wandsonborges/de0-nano-dev/cycloneV_soc/synthesis/cycloneV_soc.vhd

-- cycloneV_soc.vhd

-- Generated using ACDS version 16.1 196

library IEEE;
use IEEE.std_logic_1164.all;
use IEEE.numeric_std.all;

entity cycloneV_soc is
	port (
		adc_clk                         : out   std_logic;                                        --                     adc.clk
		clk_clk                         : in    std_logic                     := '0';             --                     clk.clk
		hps_io_hps_io_emac1_inst_TX_CLK : out   std_logic;                                        --                  hps_io.hps_io_emac1_inst_TX_CLK
		hps_io_hps_io_emac1_inst_TXD0   : out   std_logic;                                        --                        .hps_io_emac1_inst_TXD0
		hps_io_hps_io_emac1_inst_TXD1   : out   std_logic;                                        --                        .hps_io_emac1_inst_TXD1
		hps_io_hps_io_emac1_inst_TXD2   : out   std_logic;                                        --                        .hps_io_emac1_inst_TXD2
		hps_io_hps_io_emac1_inst_TXD3   : out   std_logic;                                        --                        .hps_io_emac1_inst_TXD3
		hps_io_hps_io_emac1_inst_RXD0   : in    std_logic                     := '0';             --                        .hps_io_emac1_inst_RXD0
		hps_io_hps_io_emac1_inst_MDIO   : inout std_logic                     := '0';             --                        .hps_io_emac1_inst_MDIO
		hps_io_hps_io_emac1_inst_MDC    : out   std_logic;                                        --                        .hps_io_emac1_inst_MDC
		hps_io_hps_io_emac1_inst_RX_CTL : in    std_logic                     := '0';             --                        .hps_io_emac1_inst_RX_CTL
		hps_io_hps_io_emac1_inst_TX_CTL : out   std_logic;                                        --                        .hps_io_emac1_inst_TX_CTL
		hps_io_hps_io_emac1_inst_RX_CLK : in    std_logic                     := '0';             --                        .hps_io_emac1_inst_RX_CLK
		hps_io_hps_io_emac1_inst_RXD1   : in    std_logic                     := '0';             --                        .hps_io_emac1_inst_RXD1
		hps_io_hps_io_emac1_inst_RXD2   : in    std_logic                     := '0';             --                        .hps_io_emac1_inst_RXD2
		hps_io_hps_io_emac1_inst_RXD3   : in    std_logic                     := '0';             --                        .hps_io_emac1_inst_RXD3
		hps_io_hps_io_sdio_inst_CMD     : inout std_logic                     := '0';             --                        .hps_io_sdio_inst_CMD
		hps_io_hps_io_sdio_inst_D0      : inout std_logic                     := '0';             --                        .hps_io_sdio_inst_D0
		hps_io_hps_io_sdio_inst_D1      : inout std_logic                     := '0';             --                        .hps_io_sdio_inst_D1
		hps_io_hps_io_sdio_inst_CLK     : out   std_logic;                                        --                        .hps_io_sdio_inst_CLK
		hps_io_hps_io_sdio_inst_D2      : inout std_logic                     := '0';             --                        .hps_io_sdio_inst_D2
		hps_io_hps_io_sdio_inst_D3      : inout std_logic                     := '0';             --                        .hps_io_sdio_inst_D3
		hps_io_hps_io_usb1_inst_D0      : inout std_logic                     := '0';             --                        .hps_io_usb1_inst_D0
		hps_io_hps_io_usb1_inst_D1      : inout std_logic                     := '0';             --                        .hps_io_usb1_inst_D1
		hps_io_hps_io_usb1_inst_D2      : inout std_logic                     := '0';             --                        .hps_io_usb1_inst_D2
		hps_io_hps_io_usb1_inst_D3      : inout std_logic                     := '0';             --                        .hps_io_usb1_inst_D3
		hps_io_hps_io_usb1_inst_D4      : inout std_logic                     := '0';             --                        .hps_io_usb1_inst_D4
		hps_io_hps_io_usb1_inst_D5      : inout std_logic                     := '0';             --                        .hps_io_usb1_inst_D5
		hps_io_hps_io_usb1_inst_D6      : inout std_logic                     := '0';             --                        .hps_io_usb1_inst_D6
		hps_io_hps_io_usb1_inst_D7      : inout std_logic                     := '0';             --                        .hps_io_usb1_inst_D7
		hps_io_hps_io_usb1_inst_CLK     : in    std_logic                     := '0';             --                        .hps_io_usb1_inst_CLK
		hps_io_hps_io_usb1_inst_STP     : out   std_logic;                                        --                        .hps_io_usb1_inst_STP
		hps_io_hps_io_usb1_inst_DIR     : in    std_logic                     := '0';             --                        .hps_io_usb1_inst_DIR
		hps_io_hps_io_usb1_inst_NXT     : in    std_logic                     := '0';             --                        .hps_io_usb1_inst_NXT
		hps_io_hps_io_uart0_inst_RX     : in    std_logic                     := '0';             --                        .hps_io_uart0_inst_RX
		hps_io_hps_io_uart0_inst_TX     : out   std_logic;                                        --                        .hps_io_uart0_inst_TX
		i2c_SCL                         : out   std_logic;                                        --                     i2c.SCL
		i2c_SDA                         : inout std_logic                     := '0';             --                        .SDA
		led_external_connection_export  : out   std_logic_vector(7 downto 0);                     -- led_external_connection.export
		mc_clk                          : out   std_logic;                                        --                      mc.clk
		memory_mem_a                    : out   std_logic_vector(14 downto 0);                    --                  memory.mem_a
		memory_mem_ba                   : out   std_logic_vector(2 downto 0);                     --                        .mem_ba
		memory_mem_ck                   : out   std_logic;                                        --                        .mem_ck
		memory_mem_ck_n                 : out   std_logic;                                        --                        .mem_ck_n
		memory_mem_cke                  : out   std_logic;                                        --                        .mem_cke
		memory_mem_cs_n                 : out   std_logic;                                        --                        .mem_cs_n
		memory_mem_ras_n                : out   std_logic;                                        --                        .mem_ras_n
		memory_mem_cas_n                : out   std_logic;                                        --                        .mem_cas_n
		memory_mem_we_n                 : out   std_logic;                                        --                        .mem_we_n
		memory_mem_reset_n              : out   std_logic;                                        --                        .mem_reset_n
		memory_mem_dq                   : inout std_logic_vector(31 downto 0) := (others => '0'); --                        .mem_dq
		memory_mem_dqs                  : inout std_logic_vector(3 downto 0)  := (others => '0'); --                        .mem_dqs
		memory_mem_dqs_n                : inout std_logic_vector(3 downto 0)  := (others => '0'); --                        .mem_dqs_n
		memory_mem_odt                  : out   std_logic;                                        --                        .mem_odt
		memory_mem_dm                   : out   std_logic_vector(3 downto 0);                     --                        .mem_dm
		memory_oct_rzqin                : in    std_logic                     := '0';             --                        .oct_rzqin
		pico640_PSYNC                   : in    std_logic                     := '0';             --                 pico640.PSYNC
		pico640_VSYNC                   : in    std_logic                     := '0';             --                        .VSYNC
		pico640_HSYNC                   : in    std_logic                     := '0';             --                        .HSYNC
		pico640_ADC_DATA                : in    std_logic_vector(13 downto 0) := (others => '0'); --                        .ADC_DATA
		pico640_SHUTTER                 : out   std_logic;                                        --                        .SHUTTER
		pico640_SENSOR_RST_N            : out   std_logic;                                        --                        .SENSOR_RST_N
		pico640_CLOCK_EN                : out   std_logic;                                        --                        .CLOCK_EN
		pio_export                      : out   std_logic_vector(7 downto 0);                     --                     pio.export
		reset_reset_n                   : in    std_logic                     := '0';             --                   reset.reset_n
		sw_external_connection_export   : in    std_logic_vector(3 downto 0)  := (others => '0')  --  sw_external_connection.export
	);
end entity cycloneV_soc;

architecture rtl of cycloneV_soc is
	component framewriter is
		generic (
			CLOCK_FREQ         : integer := 50000000;
			NBITS_DATA         : integer := 8;
			BURST_LENGTH_DEPTH : integer := 3;
			FIFO_DEPTH         : integer := 10
		);
		port (
			avalon_ss_clk           : in  std_logic                     := 'X';             -- clk
			avalon_mm_clk           : in  std_logic                     := 'X';             -- clk
			avalon_st_clk           : in  std_logic                     := 'X';             -- clk
			avalon_ss_rstn          : in  std_logic                     := 'X';             -- reset_n
			avalon_mm_rstn          : in  std_logic                     := 'X';             -- reset_n
			avalon_st_rstn          : in  std_logic                     := 'X';             -- reset_n
			avalon_mm_address       : out std_logic_vector(31 downto 0);                    -- address
			avalon_mm_burstcount    : out std_logic_vector(7 downto 0);                     -- burstcount
			avalon_mm_write         : out std_logic;                                        -- write
			avalon_mm_writedata     : out std_logic_vector(15 downto 0);                    -- writedata
			avalon_mm_waitrequest   : in  std_logic                     := 'X';             -- waitrequest
			avalon_ss_address       : in  std_logic_vector(2 downto 0)  := (others => 'X'); -- address
			avalon_ss_read          : in  std_logic                     := 'X';             -- read
			avalon_ss_readdata      : out std_logic_vector(31 downto 0);                    -- readdata
			avalon_ss_waitrequest   : out std_logic;                                        -- waitrequest
			avalon_ss_readdatavalid : out std_logic;                                        -- readdatavalid
			avalon_ss_write         : in  std_logic                     := 'X';             -- write
			avalon_ss_writedata     : in  std_logic_vector(31 downto 0) := (others => 'X'); -- writedata
			avalon_st_data          : in  std_logic_vector(15 downto 0) := (others => 'X'); -- data
			avalon_st_endofpacket   : in  std_logic                     := 'X';             -- endofpacket
			avalon_st_ready         : out std_logic;                                        -- ready
			avalon_st_startofpacket : in  std_logic                     := 'X';             -- startofpacket
			avalon_st_valid         : in  std_logic                     := 'X'              -- valid
		);
	end component framewriter;

	component cycloneV_soc_hps_0 is
		generic (
			F2S_Width : integer := 2;
			S2F_Width : integer := 2
		);
		port (
			mem_a                    : out   std_logic_vector(14 downto 0);                     -- mem_a
			mem_ba                   : out   std_logic_vector(2 downto 0);                      -- mem_ba
			mem_ck                   : out   std_logic;                                         -- mem_ck
			mem_ck_n                 : out   std_logic;                                         -- mem_ck_n
			mem_cke                  : out   std_logic;                                         -- mem_cke
			mem_cs_n                 : out   std_logic;                                         -- mem_cs_n
			mem_ras_n                : out   std_logic;                                         -- mem_ras_n
			mem_cas_n                : out   std_logic;                                         -- mem_cas_n
			mem_we_n                 : out   std_logic;                                         -- mem_we_n
			mem_reset_n              : out   std_logic;                                         -- mem_reset_n
			mem_dq                   : inout std_logic_vector(31 downto 0)  := (others => 'X'); -- mem_dq
			mem_dqs                  : inout std_logic_vector(3 downto 0)   := (others => 'X'); -- mem_dqs
			mem_dqs_n                : inout std_logic_vector(3 downto 0)   := (others => 'X'); -- mem_dqs_n
			mem_odt                  : out   std_logic;                                         -- mem_odt
			mem_dm                   : out   std_logic_vector(3 downto 0);                      -- mem_dm
			oct_rzqin                : in    std_logic                      := 'X';             -- oct_rzqin
			hps_io_emac1_inst_TX_CLK : out   std_logic;                                         -- hps_io_emac1_inst_TX_CLK
			hps_io_emac1_inst_TXD0   : out   std_logic;                                         -- hps_io_emac1_inst_TXD0
			hps_io_emac1_inst_TXD1   : out   std_logic;                                         -- hps_io_emac1_inst_TXD1
			hps_io_emac1_inst_TXD2   : out   std_logic;                                         -- hps_io_emac1_inst_TXD2
			hps_io_emac1_inst_TXD3   : out   std_logic;                                         -- hps_io_emac1_inst_TXD3
			hps_io_emac1_inst_RXD0   : in    std_logic                      := 'X';             -- hps_io_emac1_inst_RXD0
			hps_io_emac1_inst_MDIO   : inout std_logic                      := 'X';             -- hps_io_emac1_inst_MDIO
			hps_io_emac1_inst_MDC    : out   std_logic;                                         -- hps_io_emac1_inst_MDC
			hps_io_emac1_inst_RX_CTL : in    std_logic                      := 'X';             -- hps_io_emac1_inst_RX_CTL
			hps_io_emac1_inst_TX_CTL : out   std_logic;                                         -- hps_io_emac1_inst_TX_CTL
			hps_io_emac1_inst_RX_CLK : in    std_logic                      := 'X';             -- hps_io_emac1_inst_RX_CLK
			hps_io_emac1_inst_RXD1   : in    std_logic                      := 'X';             -- hps_io_emac1_inst_RXD1
			hps_io_emac1_inst_RXD2   : in    std_logic                      := 'X';             -- hps_io_emac1_inst_RXD2
			hps_io_emac1_inst_RXD3   : in    std_logic                      := 'X';             -- hps_io_emac1_inst_RXD3
			hps_io_sdio_inst_CMD     : inout std_logic                      := 'X';             -- hps_io_sdio_inst_CMD
			hps_io_sdio_inst_D0      : inout std_logic                      := 'X';             -- hps_io_sdio_inst_D0
			hps_io_sdio_inst_D1      : inout std_logic                      := 'X';             -- hps_io_sdio_inst_D1
			hps_io_sdio_inst_CLK     : out   std_logic;                                         -- hps_io_sdio_inst_CLK
			hps_io_sdio_inst_D2      : inout std_logic                      := 'X';             -- hps_io_sdio_inst_D2
			hps_io_sdio_inst_D3      : inout std_logic                      := 'X';             -- hps_io_sdio_inst_D3
			hps_io_usb1_inst_D0      : inout std_logic                      := 'X';             -- hps_io_usb1_inst_D0
			hps_io_usb1_inst_D1      : inout std_logic                      := 'X';             -- hps_io_usb1_inst_D1
			hps_io_usb1_inst_D2      : inout std_logic                      := 'X';             -- hps_io_usb1_inst_D2
			hps_io_usb1_inst_D3      : inout std_logic                      := 'X';             -- hps_io_usb1_inst_D3
			hps_io_usb1_inst_D4      : inout std_logic                      := 'X';             -- hps_io_usb1_inst_D4
			hps_io_usb1_inst_D5      : inout std_logic                      := 'X';             -- hps_io_usb1_inst_D5
			hps_io_usb1_inst_D6      : inout std_logic                      := 'X';             -- hps_io_usb1_inst_D6
			hps_io_usb1_inst_D7      : inout std_logic                      := 'X';             -- hps_io_usb1_inst_D7
			hps_io_usb1_inst_CLK     : in    std_logic                      := 'X';             -- hps_io_usb1_inst_CLK
			hps_io_usb1_inst_STP     : out   std_logic;                                         -- hps_io_usb1_inst_STP
			hps_io_usb1_inst_DIR     : in    std_logic                      := 'X';             -- hps_io_usb1_inst_DIR
			hps_io_usb1_inst_NXT     : in    std_logic                      := 'X';             -- hps_io_usb1_inst_NXT
			hps_io_uart0_inst_RX     : in    std_logic                      := 'X';             -- hps_io_uart0_inst_RX
			hps_io_uart0_inst_TX     : out   std_logic;                                         -- hps_io_uart0_inst_TX
			h2f_rst_n                : out   std_logic;                                         -- reset_n
			f2h_sdram0_clk           : in    std_logic                      := 'X';             -- clk
			f2h_sdram0_ADDRESS       : in    std_logic_vector(26 downto 0)  := (others => 'X'); -- address
			f2h_sdram0_BURSTCOUNT    : in    std_logic_vector(7 downto 0)   := (others => 'X'); -- burstcount
			f2h_sdram0_WAITREQUEST   : out   std_logic;                                         -- waitrequest
			f2h_sdram0_WRITEDATA     : in    std_logic_vector(255 downto 0) := (others => 'X'); -- writedata
			f2h_sdram0_BYTEENABLE    : in    std_logic_vector(31 downto 0)  := (others => 'X'); -- byteenable
			f2h_sdram0_WRITE         : in    std_logic                      := 'X';             -- write
			h2f_axi_clk              : in    std_logic                      := 'X';             -- clk
			h2f_AWID                 : out   std_logic_vector(11 downto 0);                     -- awid
			h2f_AWADDR               : out   std_logic_vector(29 downto 0);                     -- awaddr
			h2f_AWLEN                : out   std_logic_vector(3 downto 0);                      -- awlen
			h2f_AWSIZE               : out   std_logic_vector(2 downto 0);                      -- awsize
			h2f_AWBURST              : out   std_logic_vector(1 downto 0);                      -- awburst
			h2f_AWLOCK               : out   std_logic_vector(1 downto 0);                      -- awlock
			h2f_AWCACHE              : out   std_logic_vector(3 downto 0);                      -- awcache
			h2f_AWPROT               : out   std_logic_vector(2 downto 0);                      -- awprot
			h2f_AWVALID              : out   std_logic;                                         -- awvalid
			h2f_AWREADY              : in    std_logic                      := 'X';             -- awready
			h2f_WID                  : out   std_logic_vector(11 downto 0);                     -- wid
			h2f_WDATA                : out   std_logic_vector(63 downto 0);                     -- wdata
			h2f_WSTRB                : out   std_logic_vector(7 downto 0);                      -- wstrb
			h2f_WLAST                : out   std_logic;                                         -- wlast
			h2f_WVALID               : out   std_logic;                                         -- wvalid
			h2f_WREADY               : in    std_logic                      := 'X';             -- wready
			h2f_BID                  : in    std_logic_vector(11 downto 0)  := (others => 'X'); -- bid
			h2f_BRESP                : in    std_logic_vector(1 downto 0)   := (others => 'X'); -- bresp
			h2f_BVALID               : in    std_logic                      := 'X';             -- bvalid
			h2f_BREADY               : out   std_logic;                                         -- bready
			h2f_ARID                 : out   std_logic_vector(11 downto 0);                     -- arid
			h2f_ARADDR               : out   std_logic_vector(29 downto 0);                     -- araddr
			h2f_ARLEN                : out   std_logic_vector(3 downto 0);                      -- arlen
			h2f_ARSIZE               : out   std_logic_vector(2 downto 0);                      -- arsize
			h2f_ARBURST              : out   std_logic_vector(1 downto 0);                      -- arburst
			h2f_ARLOCK               : out   std_logic_vector(1 downto 0);                      -- arlock
			h2f_ARCACHE              : out   std_logic_vector(3 downto 0);                      -- arcache
			h2f_ARPROT               : out   std_logic_vector(2 downto 0);                      -- arprot
			h2f_ARVALID              : out   std_logic;                                         -- arvalid
			h2f_ARREADY              : in    std_logic                      := 'X';             -- arready
			h2f_RID                  : in    std_logic_vector(11 downto 0)  := (others => 'X'); -- rid
			h2f_RDATA                : in    std_logic_vector(63 downto 0)  := (others => 'X'); -- rdata
			h2f_RRESP                : in    std_logic_vector(1 downto 0)   := (others => 'X'); -- rresp
			h2f_RLAST                : in    std_logic                      := 'X';             -- rlast
			h2f_RVALID               : in    std_logic                      := 'X';             -- rvalid
			h2f_RREADY               : out   std_logic;                                         -- rready
			f2h_axi_clk              : in    std_logic                      := 'X';             -- clk
			f2h_AWID                 : in    std_logic_vector(7 downto 0)   := (others => 'X'); -- awid
			f2h_AWADDR               : in    std_logic_vector(31 downto 0)  := (others => 'X'); -- awaddr
			f2h_AWLEN                : in    std_logic_vector(3 downto 0)   := (others => 'X'); -- awlen
			f2h_AWSIZE               : in    std_logic_vector(2 downto 0)   := (others => 'X'); -- awsize
			f2h_AWBURST              : in    std_logic_vector(1 downto 0)   := (others => 'X'); -- awburst
			f2h_AWLOCK               : in    std_logic_vector(1 downto 0)   := (others => 'X'); -- awlock
			f2h_AWCACHE              : in    std_logic_vector(3 downto 0)   := (others => 'X'); -- awcache
			f2h_AWPROT               : in    std_logic_vector(2 downto 0)   := (others => 'X'); -- awprot
			f2h_AWVALID              : in    std_logic                      := 'X';             -- awvalid
			f2h_AWREADY              : out   std_logic;                                         -- awready
			f2h_AWUSER               : in    std_logic_vector(4 downto 0)   := (others => 'X'); -- awuser
			f2h_WID                  : in    std_logic_vector(7 downto 0)   := (others => 'X'); -- wid
			f2h_WDATA                : in    std_logic_vector(127 downto 0) := (others => 'X'); -- wdata
			f2h_WSTRB                : in    std_logic_vector(15 downto 0)  := (others => 'X'); -- wstrb
			f2h_WLAST                : in    std_logic                      := 'X';             -- wlast
			f2h_WVALID               : in    std_logic                      := 'X';             -- wvalid
			f2h_WREADY               : out   std_logic;                                         -- wready
			f2h_BID                  : out   std_logic_vector(7 downto 0);                      -- bid
			f2h_BRESP                : out   std_logic_vector(1 downto 0);                      -- bresp
			f2h_BVALID               : out   std_logic;                                         -- bvalid
			f2h_BREADY               : in    std_logic                      := 'X';             -- bready
			f2h_ARID                 : in    std_logic_vector(7 downto 0)   := (others => 'X'); -- arid
			f2h_ARADDR               : in    std_logic_vector(31 downto 0)  := (others => 'X'); -- araddr
			f2h_ARLEN                : in    std_logic_vector(3 downto 0)   := (others => 'X'); -- arlen
			f2h_ARSIZE               : in    std_logic_vector(2 downto 0)   := (others => 'X'); -- arsize
			f2h_ARBURST              : in    std_logic_vector(1 downto 0)   := (others => 'X'); -- arburst
			f2h_ARLOCK               : in    std_logic_vector(1 downto 0)   := (others => 'X'); -- arlock
			f2h_ARCACHE              : in    std_logic_vector(3 downto 0)   := (others => 'X'); -- arcache
			f2h_ARPROT               : in    std_logic_vector(2 downto 0)   := (others => 'X'); -- arprot
			f2h_ARVALID              : in    std_logic                      := 'X';             -- arvalid
			f2h_ARREADY              : out   std_logic;                                         -- arready
			f2h_ARUSER               : in    std_logic_vector(4 downto 0)   := (others => 'X'); -- aruser
			f2h_RID                  : out   std_logic_vector(7 downto 0);                      -- rid
			f2h_RDATA                : out   std_logic_vector(127 downto 0);                    -- rdata
			f2h_RRESP                : out   std_logic_vector(1 downto 0);                      -- rresp
			f2h_RLAST                : out   std_logic;                                         -- rlast
			f2h_RVALID               : out   std_logic;                                         -- rvalid
			f2h_RREADY               : in    std_logic                      := 'X';             -- rready
			h2f_lw_axi_clk           : in    std_logic                      := 'X';             -- clk
			h2f_lw_AWID              : out   std_logic_vector(11 downto 0);                     -- awid
			h2f_lw_AWADDR            : out   std_logic_vector(20 downto 0);                     -- awaddr
			h2f_lw_AWLEN             : out   std_logic_vector(3 downto 0);                      -- awlen
			h2f_lw_AWSIZE            : out   std_logic_vector(2 downto 0);                      -- awsize
			h2f_lw_AWBURST           : out   std_logic_vector(1 downto 0);                      -- awburst
			h2f_lw_AWLOCK            : out   std_logic_vector(1 downto 0);                      -- awlock
			h2f_lw_AWCACHE           : out   std_logic_vector(3 downto 0);                      -- awcache
			h2f_lw_AWPROT            : out   std_logic_vector(2 downto 0);                      -- awprot
			h2f_lw_AWVALID           : out   std_logic;                                         -- awvalid
			h2f_lw_AWREADY           : in    std_logic                      := 'X';             -- awready
			h2f_lw_WID               : out   std_logic_vector(11 downto 0);                     -- wid
			h2f_lw_WDATA             : out   std_logic_vector(31 downto 0);                     -- wdata
			h2f_lw_WSTRB             : out   std_logic_vector(3 downto 0);                      -- wstrb
			h2f_lw_WLAST             : out   std_logic;                                         -- wlast
			h2f_lw_WVALID            : out   std_logic;                                         -- wvalid
			h2f_lw_WREADY            : in    std_logic                      := 'X';             -- wready
			h2f_lw_BID               : in    std_logic_vector(11 downto 0)  := (others => 'X'); -- bid
			h2f_lw_BRESP             : in    std_logic_vector(1 downto 0)   := (others => 'X'); -- bresp
			h2f_lw_BVALID            : in    std_logic                      := 'X';             -- bvalid
			h2f_lw_BREADY            : out   std_logic;                                         -- bready
			h2f_lw_ARID              : out   std_logic_vector(11 downto 0);                     -- arid
			h2f_lw_ARADDR            : out   std_logic_vector(20 downto 0);                     -- araddr
			h2f_lw_ARLEN             : out   std_logic_vector(3 downto 0);                      -- arlen
			h2f_lw_ARSIZE            : out   std_logic_vector(2 downto 0);                      -- arsize
			h2f_lw_ARBURST           : out   std_logic_vector(1 downto 0);                      -- arburst
			h2f_lw_ARLOCK            : out   std_logic_vector(1 downto 0);                      -- arlock
			h2f_lw_ARCACHE           : out   std_logic_vector(3 downto 0);                      -- arcache
			h2f_lw_ARPROT            : out   std_logic_vector(2 downto 0);                      -- arprot
			h2f_lw_ARVALID           : out   std_logic;                                         -- arvalid
			h2f_lw_ARREADY           : in    std_logic                      := 'X';             -- arready
			h2f_lw_RID               : in    std_logic_vector(11 downto 0)  := (others => 'X'); -- rid
			h2f_lw_RDATA             : in    std_logic_vector(31 downto 0)  := (others => 'X'); -- rdata
			h2f_lw_RRESP             : in    std_logic_vector(1 downto 0)   := (others => 'X'); -- rresp
			h2f_lw_RLAST             : in    std_logic                      := 'X';             -- rlast
			h2f_lw_RVALID            : in    std_logic                      := 'X';             -- rvalid
			h2f_lw_RREADY            : out   std_logic                                          -- rready
		);
	end component cycloneV_soc_hps_0;

	component i2c_master_avalon is
		generic (
			CLOCK_FREQ   : integer := 70000000;
			I2C_CLK_FREQ : integer := 200000;
			CHECK_ACK    : boolean := true
		);
		port (
			clk                 : in    std_logic                     := 'X';             -- clk
			slave_chipselect    : in    std_logic                     := 'X';             -- chipselect
			slave_write         : in    std_logic                     := 'X';             -- write
			slave_address       : in    std_logic_vector(3 downto 0)  := (others => 'X'); -- address
			slave_writedata     : in    std_logic_vector(31 downto 0) := (others => 'X'); -- writedata
			slave_waitrequest   : out   std_logic;                                        -- waitrequest
			slave_readdatavalid : out   std_logic;                                        -- readdatavalid
			slave_readdata      : out   std_logic_vector(31 downto 0);                    -- readdata
			slave_read          : in    std_logic                     := 'X';             -- read
			rst_n               : in    std_logic                     := 'X';             -- reset_n
			SCL                 : out   std_logic;                                        -- export
			SDA                 : inout std_logic                     := 'X'              -- export
		);
	end component i2c_master_avalon;

	component cycloneV_soc_led is
		port (
			clk        : in  std_logic                     := 'X';             -- clk
			reset_n    : in  std_logic                     := 'X';             -- reset_n
			address    : in  std_logic_vector(1 downto 0)  := (others => 'X'); -- address
			write_n    : in  std_logic                     := 'X';             -- write_n
			writedata  : in  std_logic_vector(31 downto 0) := (others => 'X'); -- writedata
			chipselect : in  std_logic                     := 'X';             -- chipselect
			readdata   : out std_logic_vector(31 downto 0);                    -- readdata
			out_port   : out std_logic_vector(7 downto 0)                      -- export
		);
	end component cycloneV_soc_led;

	component pico640_avalon is
		generic (
			SENSOR_CLOCK : integer := 12000000
		);
		port (
			PSYNC                   : in  std_logic                     := 'X';             -- export
			VSYNC                   : in  std_logic                     := 'X';             -- export
			HSYNC                   : in  std_logic                     := 'X';             -- export
			ADC_DATA                : in  std_logic_vector(13 downto 0) := (others => 'X'); -- export
			SHUTTER                 : out std_logic;                                        -- export
			SENSOR_RST_N            : out std_logic;                                        -- export
			CLOCK_EN                : out std_logic;                                        -- export
			avalon_ss_clk           : in  std_logic                     := 'X';             -- clk
			master_clk              : in  std_logic                     := 'X';             -- clk
			avalon_ss_rstn          : in  std_logic                     := 'X';             -- reset_n
			master_rstn             : in  std_logic                     := 'X';             -- reset_n
			avalon_st_startofpacket : out std_logic;                                        -- startofpacket
			avalon_st_endofpacket   : out std_logic;                                        -- endofpacket
			avalon_st_valid         : out std_logic;                                        -- valid
			avalon_st_data          : out std_logic_vector(15 downto 0);                    -- data
			avalon_st_ready         : in  std_logic                     := 'X';             -- ready
			slave_write             : in  std_logic                     := 'X';             -- write
			slave_address           : in  std_logic_vector(2 downto 0)  := (others => 'X'); -- address
			slave_writedata         : in  std_logic_vector(31 downto 0) := (others => 'X'); -- writedata
			slave_waitrequest       : out std_logic;                                        -- waitrequest
			slave_readdatavalid     : out std_logic;                                        -- readdatavalid
			slave_readdata          : out std_logic_vector(31 downto 0);                    -- readdata
			slave_read              : in  std_logic                     := 'X'              -- read
		);
	end component pico640_avalon;

	component cycloneV_soc_pll_0 is
		port (
			refclk   : in  std_logic := 'X'; -- clk
			rst      : in  std_logic := 'X'; -- reset
			outclk_0 : out std_logic;        -- clk
			outclk_1 : out std_logic;        -- clk
			locked   : out std_logic         -- export
		);
	end component cycloneV_soc_pll_0;

	component cycloneV_soc_sw is
		port (
			clk      : in  std_logic                     := 'X';             -- clk
			reset_n  : in  std_logic                     := 'X';             -- reset_n
			address  : in  std_logic_vector(1 downto 0)  := (others => 'X'); -- address
			readdata : out std_logic_vector(31 downto 0);                    -- readdata
			in_port  : in  std_logic_vector(3 downto 0)  := (others => 'X')  -- export
		);
	end component cycloneV_soc_sw;

	component cycloneV_soc_mm_interconnect_0 is
		port (
			clock_50_clk_clk                                                   : in  std_logic                      := 'X';             -- clk
			framewriter_0_avalon_mm_rstn_reset_bridge_in_reset_reset           : in  std_logic                      := 'X';             -- reset
			hps_0_f2h_sdram0_data_translator_reset_reset_bridge_in_reset_reset : in  std_logic                      := 'X';             -- reset
			framewriter_0_avalon_master_address                                : in  std_logic_vector(31 downto 0)  := (others => 'X'); -- address
			framewriter_0_avalon_master_waitrequest                            : out std_logic;                                         -- waitrequest
			framewriter_0_avalon_master_burstcount                             : in  std_logic_vector(7 downto 0)   := (others => 'X'); -- burstcount
			framewriter_0_avalon_master_write                                  : in  std_logic                      := 'X';             -- write
			framewriter_0_avalon_master_writedata                              : in  std_logic_vector(15 downto 0)  := (others => 'X'); -- writedata
			hps_0_f2h_sdram0_data_address                                      : out std_logic_vector(26 downto 0);                     -- address
			hps_0_f2h_sdram0_data_write                                        : out std_logic;                                         -- write
			hps_0_f2h_sdram0_data_writedata                                    : out std_logic_vector(255 downto 0);                    -- writedata
			hps_0_f2h_sdram0_data_burstcount                                   : out std_logic_vector(7 downto 0);                      -- burstcount
			hps_0_f2h_sdram0_data_byteenable                                   : out std_logic_vector(31 downto 0);                     -- byteenable
			hps_0_f2h_sdram0_data_waitrequest                                  : in  std_logic                      := 'X'              -- waitrequest
		);
	end component cycloneV_soc_mm_interconnect_0;

	component cycloneV_soc_mm_interconnect_1 is
		port (
			hps_0_h2f_lw_axi_master_awid                                        : in  std_logic_vector(11 downto 0) := (others => 'X'); -- awid
			hps_0_h2f_lw_axi_master_awaddr                                      : in  std_logic_vector(20 downto 0) := (others => 'X'); -- awaddr
			hps_0_h2f_lw_axi_master_awlen                                       : in  std_logic_vector(3 downto 0)  := (others => 'X'); -- awlen
			hps_0_h2f_lw_axi_master_awsize                                      : in  std_logic_vector(2 downto 0)  := (others => 'X'); -- awsize
			hps_0_h2f_lw_axi_master_awburst                                     : in  std_logic_vector(1 downto 0)  := (others => 'X'); -- awburst
			hps_0_h2f_lw_axi_master_awlock                                      : in  std_logic_vector(1 downto 0)  := (others => 'X'); -- awlock
			hps_0_h2f_lw_axi_master_awcache                                     : in  std_logic_vector(3 downto 0)  := (others => 'X'); -- awcache
			hps_0_h2f_lw_axi_master_awprot                                      : in  std_logic_vector(2 downto 0)  := (others => 'X'); -- awprot
			hps_0_h2f_lw_axi_master_awvalid                                     : in  std_logic                     := 'X';             -- awvalid
			hps_0_h2f_lw_axi_master_awready                                     : out std_logic;                                        -- awready
			hps_0_h2f_lw_axi_master_wid                                         : in  std_logic_vector(11 downto 0) := (others => 'X'); -- wid
			hps_0_h2f_lw_axi_master_wdata                                       : in  std_logic_vector(31 downto 0) := (others => 'X'); -- wdata
			hps_0_h2f_lw_axi_master_wstrb                                       : in  std_logic_vector(3 downto 0)  := (others => 'X'); -- wstrb
			hps_0_h2f_lw_axi_master_wlast                                       : in  std_logic                     := 'X';             -- wlast
			hps_0_h2f_lw_axi_master_wvalid                                      : in  std_logic                     := 'X';             -- wvalid
			hps_0_h2f_lw_axi_master_wready                                      : out std_logic;                                        -- wready
			hps_0_h2f_lw_axi_master_bid                                         : out std_logic_vector(11 downto 0);                    -- bid
			hps_0_h2f_lw_axi_master_bresp                                       : out std_logic_vector(1 downto 0);                     -- bresp
			hps_0_h2f_lw_axi_master_bvalid                                      : out std_logic;                                        -- bvalid
			hps_0_h2f_lw_axi_master_bready                                      : in  std_logic                     := 'X';             -- bready
			hps_0_h2f_lw_axi_master_arid                                        : in  std_logic_vector(11 downto 0) := (others => 'X'); -- arid
			hps_0_h2f_lw_axi_master_araddr                                      : in  std_logic_vector(20 downto 0) := (others => 'X'); -- araddr
			hps_0_h2f_lw_axi_master_arlen                                       : in  std_logic_vector(3 downto 0)  := (others => 'X'); -- arlen
			hps_0_h2f_lw_axi_master_arsize                                      : in  std_logic_vector(2 downto 0)  := (others => 'X'); -- arsize
			hps_0_h2f_lw_axi_master_arburst                                     : in  std_logic_vector(1 downto 0)  := (others => 'X'); -- arburst
			hps_0_h2f_lw_axi_master_arlock                                      : in  std_logic_vector(1 downto 0)  := (others => 'X'); -- arlock
			hps_0_h2f_lw_axi_master_arcache                                     : in  std_logic_vector(3 downto 0)  := (others => 'X'); -- arcache
			hps_0_h2f_lw_axi_master_arprot                                      : in  std_logic_vector(2 downto 0)  := (others => 'X'); -- arprot
			hps_0_h2f_lw_axi_master_arvalid                                     : in  std_logic                     := 'X';             -- arvalid
			hps_0_h2f_lw_axi_master_arready                                     : out std_logic;                                        -- arready
			hps_0_h2f_lw_axi_master_rid                                         : out std_logic_vector(11 downto 0);                    -- rid
			hps_0_h2f_lw_axi_master_rdata                                       : out std_logic_vector(31 downto 0);                    -- rdata
			hps_0_h2f_lw_axi_master_rresp                                       : out std_logic_vector(1 downto 0);                     -- rresp
			hps_0_h2f_lw_axi_master_rlast                                       : out std_logic;                                        -- rlast
			hps_0_h2f_lw_axi_master_rvalid                                      : out std_logic;                                        -- rvalid
			hps_0_h2f_lw_axi_master_rready                                      : in  std_logic                     := 'X';             -- rready
			clock_50_clk_clk                                                    : in  std_logic                     := 'X';             -- clk
			framewriter_0_avalon_ss_rstn_reset_bridge_in_reset_reset            : in  std_logic                     := 'X';             -- reset
			hps_0_h2f_lw_axi_master_agent_clk_reset_reset_bridge_in_reset_reset : in  std_logic                     := 'X';             -- reset
			framewriter_0_avalon_slave_address                                  : out std_logic_vector(2 downto 0);                     -- address
			framewriter_0_avalon_slave_write                                    : out std_logic;                                        -- write
			framewriter_0_avalon_slave_read                                     : out std_logic;                                        -- read
			framewriter_0_avalon_slave_readdata                                 : in  std_logic_vector(31 downto 0) := (others => 'X'); -- readdata
			framewriter_0_avalon_slave_writedata                                : out std_logic_vector(31 downto 0);                    -- writedata
			framewriter_0_avalon_slave_readdatavalid                            : in  std_logic                     := 'X';             -- readdatavalid
			framewriter_0_avalon_slave_waitrequest                              : in  std_logic                     := 'X';             -- waitrequest
			i2c_master_avalon_0_slave_address                                   : out std_logic_vector(3 downto 0);                     -- address
			i2c_master_avalon_0_slave_write                                     : out std_logic;                                        -- write
			i2c_master_avalon_0_slave_read                                      : out std_logic;                                        -- read
			i2c_master_avalon_0_slave_readdata                                  : in  std_logic_vector(31 downto 0) := (others => 'X'); -- readdata
			i2c_master_avalon_0_slave_writedata                                 : out std_logic_vector(31 downto 0);                    -- writedata
			i2c_master_avalon_0_slave_readdatavalid                             : in  std_logic                     := 'X';             -- readdatavalid
			i2c_master_avalon_0_slave_waitrequest                               : in  std_logic                     := 'X';             -- waitrequest
			i2c_master_avalon_0_slave_chipselect                                : out std_logic;                                        -- chipselect
			led_s1_address                                                      : out std_logic_vector(1 downto 0);                     -- address
			led_s1_write                                                        : out std_logic;                                        -- write
			led_s1_readdata                                                     : in  std_logic_vector(31 downto 0) := (others => 'X'); -- readdata
			led_s1_writedata                                                    : out std_logic_vector(31 downto 0);                    -- writedata
			led_s1_chipselect                                                   : out std_logic;                                        -- chipselect
			pico640_ctrl_0_avalon_slave_address                                 : out std_logic_vector(2 downto 0);                     -- address
			pico640_ctrl_0_avalon_slave_write                                   : out std_logic;                                        -- write
			pico640_ctrl_0_avalon_slave_read                                    : out std_logic;                                        -- read
			pico640_ctrl_0_avalon_slave_readdata                                : in  std_logic_vector(31 downto 0) := (others => 'X'); -- readdata
			pico640_ctrl_0_avalon_slave_writedata                               : out std_logic_vector(31 downto 0);                    -- writedata
			pico640_ctrl_0_avalon_slave_readdatavalid                           : in  std_logic                     := 'X';             -- readdatavalid
			pico640_ctrl_0_avalon_slave_waitrequest                             : in  std_logic                     := 'X';             -- waitrequest
			pio_0_s1_address                                                    : out std_logic_vector(1 downto 0);                     -- address
			pio_0_s1_write                                                      : out std_logic;                                        -- write
			pio_0_s1_readdata                                                   : in  std_logic_vector(31 downto 0) := (others => 'X'); -- readdata
			pio_0_s1_writedata                                                  : out std_logic_vector(31 downto 0);                    -- writedata
			pio_0_s1_chipselect                                                 : out std_logic;                                        -- chipselect
			sw_s1_address                                                       : out std_logic_vector(1 downto 0);                     -- address
			sw_s1_readdata                                                      : in  std_logic_vector(31 downto 0) := (others => 'X')  -- readdata
		);
	end component cycloneV_soc_mm_interconnect_1;

	component altera_reset_controller is
		generic (
			NUM_RESET_INPUTS          : integer := 6;
			OUTPUT_RESET_SYNC_EDGES   : string  := "deassert";
			SYNC_DEPTH                : integer := 2;
			RESET_REQUEST_PRESENT     : integer := 0;
			RESET_REQ_WAIT_TIME       : integer := 1;
			MIN_RST_ASSERTION_TIME    : integer := 3;
			RESET_REQ_EARLY_DSRT_TIME : integer := 1;
			USE_RESET_REQUEST_IN0     : integer := 0;
			USE_RESET_REQUEST_IN1     : integer := 0;
			USE_RESET_REQUEST_IN2     : integer := 0;
			USE_RESET_REQUEST_IN3     : integer := 0;
			USE_RESET_REQUEST_IN4     : integer := 0;
			USE_RESET_REQUEST_IN5     : integer := 0;
			USE_RESET_REQUEST_IN6     : integer := 0;
			USE_RESET_REQUEST_IN7     : integer := 0;
			USE_RESET_REQUEST_IN8     : integer := 0;
			USE_RESET_REQUEST_IN9     : integer := 0;
			USE_RESET_REQUEST_IN10    : integer := 0;
			USE_RESET_REQUEST_IN11    : integer := 0;
			USE_RESET_REQUEST_IN12    : integer := 0;
			USE_RESET_REQUEST_IN13    : integer := 0;
			USE_RESET_REQUEST_IN14    : integer := 0;
			USE_RESET_REQUEST_IN15    : integer := 0;
			ADAPT_RESET_REQUEST       : integer := 0
		);
		port (
			reset_in0      : in  std_logic := 'X'; -- reset
			clk            : in  std_logic := 'X'; -- clk
			reset_out      : out std_logic;        -- reset
			reset_req      : out std_logic;        -- reset_req
			reset_req_in0  : in  std_logic := 'X'; -- reset_req
			reset_in1      : in  std_logic := 'X'; -- reset
			reset_req_in1  : in  std_logic := 'X'; -- reset_req
			reset_in2      : in  std_logic := 'X'; -- reset
			reset_req_in2  : in  std_logic := 'X'; -- reset_req
			reset_in3      : in  std_logic := 'X'; -- reset
			reset_req_in3  : in  std_logic := 'X'; -- reset_req
			reset_in4      : in  std_logic := 'X'; -- reset
			reset_req_in4  : in  std_logic := 'X'; -- reset_req
			reset_in5      : in  std_logic := 'X'; -- reset
			reset_req_in5  : in  std_logic := 'X'; -- reset_req
			reset_in6      : in  std_logic := 'X'; -- reset
			reset_req_in6  : in  std_logic := 'X'; -- reset_req
			reset_in7      : in  std_logic := 'X'; -- reset
			reset_req_in7  : in  std_logic := 'X'; -- reset_req
			reset_in8      : in  std_logic := 'X'; -- reset
			reset_req_in8  : in  std_logic := 'X'; -- reset_req
			reset_in9      : in  std_logic := 'X'; -- reset
			reset_req_in9  : in  std_logic := 'X'; -- reset_req
			reset_in10     : in  std_logic := 'X'; -- reset
			reset_req_in10 : in  std_logic := 'X'; -- reset_req
			reset_in11     : in  std_logic := 'X'; -- reset
			reset_req_in11 : in  std_logic := 'X'; -- reset_req
			reset_in12     : in  std_logic := 'X'; -- reset
			reset_req_in12 : in  std_logic := 'X'; -- reset_req
			reset_in13     : in  std_logic := 'X'; -- reset
			reset_req_in13 : in  std_logic := 'X'; -- reset_req
			reset_in14     : in  std_logic := 'X'; -- reset
			reset_req_in14 : in  std_logic := 'X'; -- reset_req
			reset_in15     : in  std_logic := 'X'; -- reset
			reset_req_in15 : in  std_logic := 'X'  -- reset_req
		);
	end component altera_reset_controller;

	signal pico640_ctrl_0_avalon_st_out_valid                          : std_logic;                      -- pico640_ctrl_0:avalon_st_valid -> framewriter_0:avalon_st_valid
	signal pico640_ctrl_0_avalon_st_out_data                           : std_logic_vector(15 downto 0);  -- pico640_ctrl_0:avalon_st_data -> framewriter_0:avalon_st_data
	signal pico640_ctrl_0_avalon_st_out_ready                          : std_logic;                      -- framewriter_0:avalon_st_ready -> pico640_ctrl_0:avalon_st_ready
	signal pico640_ctrl_0_avalon_st_out_startofpacket                  : std_logic;                      -- pico640_ctrl_0:avalon_st_startofpacket -> framewriter_0:avalon_st_startofpacket
	signal pico640_ctrl_0_avalon_st_out_endofpacket                    : std_logic;                      -- pico640_ctrl_0:avalon_st_endofpacket -> framewriter_0:avalon_st_endofpacket
	signal pll_0_outclk0_clk                                           : std_logic;                      -- pll_0:outclk_0 -> [mc_clk, framewriter_0:avalon_st_clk, pico640_ctrl_0:master_clk, rst_controller_001:clk]
	signal framewriter_0_avalon_master_waitrequest                     : std_logic;                      -- mm_interconnect_0:framewriter_0_avalon_master_waitrequest -> framewriter_0:avalon_mm_waitrequest
	signal framewriter_0_avalon_master_address                         : std_logic_vector(31 downto 0);  -- framewriter_0:avalon_mm_address -> mm_interconnect_0:framewriter_0_avalon_master_address
	signal framewriter_0_avalon_master_write                           : std_logic;                      -- framewriter_0:avalon_mm_write -> mm_interconnect_0:framewriter_0_avalon_master_write
	signal framewriter_0_avalon_master_writedata                       : std_logic_vector(15 downto 0);  -- framewriter_0:avalon_mm_writedata -> mm_interconnect_0:framewriter_0_avalon_master_writedata
	signal framewriter_0_avalon_master_burstcount                      : std_logic_vector(7 downto 0);   -- framewriter_0:avalon_mm_burstcount -> mm_interconnect_0:framewriter_0_avalon_master_burstcount
	signal mm_interconnect_0_hps_0_f2h_sdram0_data_waitrequest         : std_logic;                      -- hps_0:f2h_sdram0_WAITREQUEST -> mm_interconnect_0:hps_0_f2h_sdram0_data_waitrequest
	signal mm_interconnect_0_hps_0_f2h_sdram0_data_address             : std_logic_vector(26 downto 0);  -- mm_interconnect_0:hps_0_f2h_sdram0_data_address -> hps_0:f2h_sdram0_ADDRESS
	signal mm_interconnect_0_hps_0_f2h_sdram0_data_byteenable          : std_logic_vector(31 downto 0);  -- mm_interconnect_0:hps_0_f2h_sdram0_data_byteenable -> hps_0:f2h_sdram0_BYTEENABLE
	signal mm_interconnect_0_hps_0_f2h_sdram0_data_write               : std_logic;                      -- mm_interconnect_0:hps_0_f2h_sdram0_data_write -> hps_0:f2h_sdram0_WRITE
	signal mm_interconnect_0_hps_0_f2h_sdram0_data_writedata           : std_logic_vector(255 downto 0); -- mm_interconnect_0:hps_0_f2h_sdram0_data_writedata -> hps_0:f2h_sdram0_WRITEDATA
	signal mm_interconnect_0_hps_0_f2h_sdram0_data_burstcount          : std_logic_vector(7 downto 0);   -- mm_interconnect_0:hps_0_f2h_sdram0_data_burstcount -> hps_0:f2h_sdram0_BURSTCOUNT
	signal hps_0_h2f_lw_axi_master_awburst                             : std_logic_vector(1 downto 0);   -- hps_0:h2f_lw_AWBURST -> mm_interconnect_1:hps_0_h2f_lw_axi_master_awburst
	signal hps_0_h2f_lw_axi_master_arlen                               : std_logic_vector(3 downto 0);   -- hps_0:h2f_lw_ARLEN -> mm_interconnect_1:hps_0_h2f_lw_axi_master_arlen
	signal hps_0_h2f_lw_axi_master_wstrb                               : std_logic_vector(3 downto 0);   -- hps_0:h2f_lw_WSTRB -> mm_interconnect_1:hps_0_h2f_lw_axi_master_wstrb
	signal hps_0_h2f_lw_axi_master_wready                              : std_logic;                      -- mm_interconnect_1:hps_0_h2f_lw_axi_master_wready -> hps_0:h2f_lw_WREADY
	signal hps_0_h2f_lw_axi_master_rid                                 : std_logic_vector(11 downto 0);  -- mm_interconnect_1:hps_0_h2f_lw_axi_master_rid -> hps_0:h2f_lw_RID
	signal hps_0_h2f_lw_axi_master_rready                              : std_logic;                      -- hps_0:h2f_lw_RREADY -> mm_interconnect_1:hps_0_h2f_lw_axi_master_rready
	signal hps_0_h2f_lw_axi_master_awlen                               : std_logic_vector(3 downto 0);   -- hps_0:h2f_lw_AWLEN -> mm_interconnect_1:hps_0_h2f_lw_axi_master_awlen
	signal hps_0_h2f_lw_axi_master_wid                                 : std_logic_vector(11 downto 0);  -- hps_0:h2f_lw_WID -> mm_interconnect_1:hps_0_h2f_lw_axi_master_wid
	signal hps_0_h2f_lw_axi_master_arcache                             : std_logic_vector(3 downto 0);   -- hps_0:h2f_lw_ARCACHE -> mm_interconnect_1:hps_0_h2f_lw_axi_master_arcache
	signal hps_0_h2f_lw_axi_master_wvalid                              : std_logic;                      -- hps_0:h2f_lw_WVALID -> mm_interconnect_1:hps_0_h2f_lw_axi_master_wvalid
	signal hps_0_h2f_lw_axi_master_araddr                              : std_logic_vector(20 downto 0);  -- hps_0:h2f_lw_ARADDR -> mm_interconnect_1:hps_0_h2f_lw_axi_master_araddr
	signal hps_0_h2f_lw_axi_master_arprot                              : std_logic_vector(2 downto 0);   -- hps_0:h2f_lw_ARPROT -> mm_interconnect_1:hps_0_h2f_lw_axi_master_arprot
	signal hps_0_h2f_lw_axi_master_awprot                              : std_logic_vector(2 downto 0);   -- hps_0:h2f_lw_AWPROT -> mm_interconnect_1:hps_0_h2f_lw_axi_master_awprot
	signal hps_0_h2f_lw_axi_master_wdata                               : std_logic_vector(31 downto 0);  -- hps_0:h2f_lw_WDATA -> mm_interconnect_1:hps_0_h2f_lw_axi_master_wdata
	signal hps_0_h2f_lw_axi_master_arvalid                             : std_logic;                      -- hps_0:h2f_lw_ARVALID -> mm_interconnect_1:hps_0_h2f_lw_axi_master_arvalid
	signal hps_0_h2f_lw_axi_master_awcache                             : std_logic_vector(3 downto 0);   -- hps_0:h2f_lw_AWCACHE -> mm_interconnect_1:hps_0_h2f_lw_axi_master_awcache
	signal hps_0_h2f_lw_axi_master_arid                                : std_logic_vector(11 downto 0);  -- hps_0:h2f_lw_ARID -> mm_interconnect_1:hps_0_h2f_lw_axi_master_arid
	signal hps_0_h2f_lw_axi_master_arlock                              : std_logic_vector(1 downto 0);   -- hps_0:h2f_lw_ARLOCK -> mm_interconnect_1:hps_0_h2f_lw_axi_master_arlock
	signal hps_0_h2f_lw_axi_master_awlock                              : std_logic_vector(1 downto 0);   -- hps_0:h2f_lw_AWLOCK -> mm_interconnect_1:hps_0_h2f_lw_axi_master_awlock
	signal hps_0_h2f_lw_axi_master_awaddr                              : std_logic_vector(20 downto 0);  -- hps_0:h2f_lw_AWADDR -> mm_interconnect_1:hps_0_h2f_lw_axi_master_awaddr
	signal hps_0_h2f_lw_axi_master_bresp                               : std_logic_vector(1 downto 0);   -- mm_interconnect_1:hps_0_h2f_lw_axi_master_bresp -> hps_0:h2f_lw_BRESP
	signal hps_0_h2f_lw_axi_master_arready                             : std_logic;                      -- mm_interconnect_1:hps_0_h2f_lw_axi_master_arready -> hps_0:h2f_lw_ARREADY
	signal hps_0_h2f_lw_axi_master_rdata                               : std_logic_vector(31 downto 0);  -- mm_interconnect_1:hps_0_h2f_lw_axi_master_rdata -> hps_0:h2f_lw_RDATA
	signal hps_0_h2f_lw_axi_master_awready                             : std_logic;                      -- mm_interconnect_1:hps_0_h2f_lw_axi_master_awready -> hps_0:h2f_lw_AWREADY
	signal hps_0_h2f_lw_axi_master_arburst                             : std_logic_vector(1 downto 0);   -- hps_0:h2f_lw_ARBURST -> mm_interconnect_1:hps_0_h2f_lw_axi_master_arburst
	signal hps_0_h2f_lw_axi_master_arsize                              : std_logic_vector(2 downto 0);   -- hps_0:h2f_lw_ARSIZE -> mm_interconnect_1:hps_0_h2f_lw_axi_master_arsize
	signal hps_0_h2f_lw_axi_master_bready                              : std_logic;                      -- hps_0:h2f_lw_BREADY -> mm_interconnect_1:hps_0_h2f_lw_axi_master_bready
	signal hps_0_h2f_lw_axi_master_rlast                               : std_logic;                      -- mm_interconnect_1:hps_0_h2f_lw_axi_master_rlast -> hps_0:h2f_lw_RLAST
	signal hps_0_h2f_lw_axi_master_wlast                               : std_logic;                      -- hps_0:h2f_lw_WLAST -> mm_interconnect_1:hps_0_h2f_lw_axi_master_wlast
	signal hps_0_h2f_lw_axi_master_rresp                               : std_logic_vector(1 downto 0);   -- mm_interconnect_1:hps_0_h2f_lw_axi_master_rresp -> hps_0:h2f_lw_RRESP
	signal hps_0_h2f_lw_axi_master_awid                                : std_logic_vector(11 downto 0);  -- hps_0:h2f_lw_AWID -> mm_interconnect_1:hps_0_h2f_lw_axi_master_awid
	signal hps_0_h2f_lw_axi_master_bid                                 : std_logic_vector(11 downto 0);  -- mm_interconnect_1:hps_0_h2f_lw_axi_master_bid -> hps_0:h2f_lw_BID
	signal hps_0_h2f_lw_axi_master_bvalid                              : std_logic;                      -- mm_interconnect_1:hps_0_h2f_lw_axi_master_bvalid -> hps_0:h2f_lw_BVALID
	signal hps_0_h2f_lw_axi_master_awsize                              : std_logic_vector(2 downto 0);   -- hps_0:h2f_lw_AWSIZE -> mm_interconnect_1:hps_0_h2f_lw_axi_master_awsize
	signal hps_0_h2f_lw_axi_master_awvalid                             : std_logic;                      -- hps_0:h2f_lw_AWVALID -> mm_interconnect_1:hps_0_h2f_lw_axi_master_awvalid
	signal hps_0_h2f_lw_axi_master_rvalid                              : std_logic;                      -- mm_interconnect_1:hps_0_h2f_lw_axi_master_rvalid -> hps_0:h2f_lw_RVALID
	signal mm_interconnect_1_framewriter_0_avalon_slave_readdata       : std_logic_vector(31 downto 0);  -- framewriter_0:avalon_ss_readdata -> mm_interconnect_1:framewriter_0_avalon_slave_readdata
	signal mm_interconnect_1_framewriter_0_avalon_slave_waitrequest    : std_logic;                      -- framewriter_0:avalon_ss_waitrequest -> mm_interconnect_1:framewriter_0_avalon_slave_waitrequest
	signal mm_interconnect_1_framewriter_0_avalon_slave_address        : std_logic_vector(2 downto 0);   -- mm_interconnect_1:framewriter_0_avalon_slave_address -> framewriter_0:avalon_ss_address
	signal mm_interconnect_1_framewriter_0_avalon_slave_read           : std_logic;                      -- mm_interconnect_1:framewriter_0_avalon_slave_read -> framewriter_0:avalon_ss_read
	signal mm_interconnect_1_framewriter_0_avalon_slave_readdatavalid  : std_logic;                      -- framewriter_0:avalon_ss_readdatavalid -> mm_interconnect_1:framewriter_0_avalon_slave_readdatavalid
	signal mm_interconnect_1_framewriter_0_avalon_slave_write          : std_logic;                      -- mm_interconnect_1:framewriter_0_avalon_slave_write -> framewriter_0:avalon_ss_write
	signal mm_interconnect_1_framewriter_0_avalon_slave_writedata      : std_logic_vector(31 downto 0);  -- mm_interconnect_1:framewriter_0_avalon_slave_writedata -> framewriter_0:avalon_ss_writedata
	signal mm_interconnect_1_pico640_ctrl_0_avalon_slave_readdata      : std_logic_vector(31 downto 0);  -- pico640_ctrl_0:slave_readdata -> mm_interconnect_1:pico640_ctrl_0_avalon_slave_readdata
	signal mm_interconnect_1_pico640_ctrl_0_avalon_slave_waitrequest   : std_logic;                      -- pico640_ctrl_0:slave_waitrequest -> mm_interconnect_1:pico640_ctrl_0_avalon_slave_waitrequest
	signal mm_interconnect_1_pico640_ctrl_0_avalon_slave_address       : std_logic_vector(2 downto 0);   -- mm_interconnect_1:pico640_ctrl_0_avalon_slave_address -> pico640_ctrl_0:slave_address
	signal mm_interconnect_1_pico640_ctrl_0_avalon_slave_read          : std_logic;                      -- mm_interconnect_1:pico640_ctrl_0_avalon_slave_read -> pico640_ctrl_0:slave_read
	signal mm_interconnect_1_pico640_ctrl_0_avalon_slave_readdatavalid : std_logic;                      -- pico640_ctrl_0:slave_readdatavalid -> mm_interconnect_1:pico640_ctrl_0_avalon_slave_readdatavalid
	signal mm_interconnect_1_pico640_ctrl_0_avalon_slave_write         : std_logic;                      -- mm_interconnect_1:pico640_ctrl_0_avalon_slave_write -> pico640_ctrl_0:slave_write
	signal mm_interconnect_1_pico640_ctrl_0_avalon_slave_writedata     : std_logic_vector(31 downto 0);  -- mm_interconnect_1:pico640_ctrl_0_avalon_slave_writedata -> pico640_ctrl_0:slave_writedata
	signal mm_interconnect_1_sw_s1_readdata                            : std_logic_vector(31 downto 0);  -- sw:readdata -> mm_interconnect_1:sw_s1_readdata
	signal mm_interconnect_1_sw_s1_address                             : std_logic_vector(1 downto 0);   -- mm_interconnect_1:sw_s1_address -> sw:address
	signal mm_interconnect_1_led_s1_chipselect                         : std_logic;                      -- mm_interconnect_1:led_s1_chipselect -> led:chipselect
	signal mm_interconnect_1_led_s1_readdata                           : std_logic_vector(31 downto 0);  -- led:readdata -> mm_interconnect_1:led_s1_readdata
	signal mm_interconnect_1_led_s1_address                            : std_logic_vector(1 downto 0);   -- mm_interconnect_1:led_s1_address -> led:address
	signal mm_interconnect_1_led_s1_write                              : std_logic;                      -- mm_interconnect_1:led_s1_write -> mm_interconnect_1_led_s1_write:in
	signal mm_interconnect_1_led_s1_writedata                          : std_logic_vector(31 downto 0);  -- mm_interconnect_1:led_s1_writedata -> led:writedata
	signal mm_interconnect_1_pio_0_s1_chipselect                       : std_logic;                      -- mm_interconnect_1:pio_0_s1_chipselect -> pio_0:chipselect
	signal mm_interconnect_1_pio_0_s1_readdata                         : std_logic_vector(31 downto 0);  -- pio_0:readdata -> mm_interconnect_1:pio_0_s1_readdata
	signal mm_interconnect_1_pio_0_s1_address                          : std_logic_vector(1 downto 0);   -- mm_interconnect_1:pio_0_s1_address -> pio_0:address
	signal mm_interconnect_1_pio_0_s1_write                            : std_logic;                      -- mm_interconnect_1:pio_0_s1_write -> mm_interconnect_1_pio_0_s1_write:in
	signal mm_interconnect_1_pio_0_s1_writedata                        : std_logic_vector(31 downto 0);  -- mm_interconnect_1:pio_0_s1_writedata -> pio_0:writedata
	signal mm_interconnect_1_i2c_master_avalon_0_slave_chipselect      : std_logic;                      -- mm_interconnect_1:i2c_master_avalon_0_slave_chipselect -> i2c_master_avalon_0:slave_chipselect
	signal mm_interconnect_1_i2c_master_avalon_0_slave_readdata        : std_logic_vector(31 downto 0);  -- i2c_master_avalon_0:slave_readdata -> mm_interconnect_1:i2c_master_avalon_0_slave_readdata
	signal mm_interconnect_1_i2c_master_avalon_0_slave_waitrequest     : std_logic;                      -- i2c_master_avalon_0:slave_waitrequest -> mm_interconnect_1:i2c_master_avalon_0_slave_waitrequest
	signal mm_interconnect_1_i2c_master_avalon_0_slave_address         : std_logic_vector(3 downto 0);   -- mm_interconnect_1:i2c_master_avalon_0_slave_address -> i2c_master_avalon_0:slave_address
	signal mm_interconnect_1_i2c_master_avalon_0_slave_read            : std_logic;                      -- mm_interconnect_1:i2c_master_avalon_0_slave_read -> i2c_master_avalon_0:slave_read
	signal mm_interconnect_1_i2c_master_avalon_0_slave_readdatavalid   : std_logic;                      -- i2c_master_avalon_0:slave_readdatavalid -> mm_interconnect_1:i2c_master_avalon_0_slave_readdatavalid
	signal mm_interconnect_1_i2c_master_avalon_0_slave_write           : std_logic;                      -- mm_interconnect_1:i2c_master_avalon_0_slave_write -> i2c_master_avalon_0:slave_write
	signal mm_interconnect_1_i2c_master_avalon_0_slave_writedata       : std_logic_vector(31 downto 0);  -- mm_interconnect_1:i2c_master_avalon_0_slave_writedata -> i2c_master_avalon_0:slave_writedata
	signal rst_controller_reset_out_reset                              : std_logic;                      -- rst_controller:reset_out -> [mm_interconnect_0:framewriter_0_avalon_mm_rstn_reset_bridge_in_reset_reset, mm_interconnect_1:framewriter_0_avalon_ss_rstn_reset_bridge_in_reset_reset, rst_controller_reset_out_reset:in]
	signal rst_controller_001_reset_out_reset                          : std_logic;                      -- rst_controller_001:reset_out -> rst_controller_001_reset_out_reset:in
	signal rst_controller_002_reset_out_reset                          : std_logic;                      -- rst_controller_002:reset_out -> [mm_interconnect_0:hps_0_f2h_sdram0_data_translator_reset_reset_bridge_in_reset_reset, mm_interconnect_1:hps_0_h2f_lw_axi_master_agent_clk_reset_reset_bridge_in_reset_reset]
	signal hps_0_h2f_reset_reset                                       : std_logic;                      -- hps_0:h2f_rst_n -> hps_0_h2f_reset_reset:in
	signal reset_reset_n_ports_inv                                     : std_logic;                      -- reset_reset_n:inv -> [pll_0:rst, rst_controller:reset_in0, rst_controller_001:reset_in0]
	signal mm_interconnect_1_led_s1_write_ports_inv                    : std_logic;                      -- mm_interconnect_1_led_s1_write:inv -> led:write_n
	signal mm_interconnect_1_pio_0_s1_write_ports_inv                  : std_logic;                      -- mm_interconnect_1_pio_0_s1_write:inv -> pio_0:write_n
	signal rst_controller_reset_out_reset_ports_inv                    : std_logic;                      -- rst_controller_reset_out_reset:inv -> [framewriter_0:avalon_mm_rstn, framewriter_0:avalon_ss_rstn, i2c_master_avalon_0:rst_n, led:reset_n, pico640_ctrl_0:avalon_ss_rstn, pio_0:reset_n, sw:reset_n]
	signal rst_controller_001_reset_out_reset_ports_inv                : std_logic;                      -- rst_controller_001_reset_out_reset:inv -> [framewriter_0:avalon_st_rstn, pico640_ctrl_0:master_rstn]
	signal hps_0_h2f_reset_reset_ports_inv                             : std_logic;                      -- hps_0_h2f_reset_reset:inv -> rst_controller_002:reset_in0

begin

	framewriter_0 : component framewriter
		generic map (
			CLOCK_FREQ         => 50000000,
			NBITS_DATA         => 16,
			BURST_LENGTH_DEPTH => 3,
			FIFO_DEPTH         => 10
		)
		port map (
			avalon_ss_clk           => clk_clk,                                                    --  avalon_ss_clk.clk
			avalon_mm_clk           => clk_clk,                                                    --  avalon_mm_clk.clk
			avalon_st_clk           => pll_0_outclk0_clk,                                          --  avalon_st_clk.clk
			avalon_ss_rstn          => rst_controller_reset_out_reset_ports_inv,                   -- avalon_ss_rstn.reset_n
			avalon_mm_rstn          => rst_controller_reset_out_reset_ports_inv,                   -- avalon_mm_rstn.reset_n
			avalon_st_rstn          => rst_controller_001_reset_out_reset_ports_inv,               -- avalon_st_rstn.reset_n
			avalon_mm_address       => framewriter_0_avalon_master_address,                        --  avalon_master.address
			avalon_mm_burstcount    => framewriter_0_avalon_master_burstcount,                     --               .burstcount
			avalon_mm_write         => framewriter_0_avalon_master_write,                          --               .write
			avalon_mm_writedata     => framewriter_0_avalon_master_writedata,                      --               .writedata
			avalon_mm_waitrequest   => framewriter_0_avalon_master_waitrequest,                    --               .waitrequest
			avalon_ss_address       => mm_interconnect_1_framewriter_0_avalon_slave_address,       --   avalon_slave.address
			avalon_ss_read          => mm_interconnect_1_framewriter_0_avalon_slave_read,          --               .read
			avalon_ss_readdata      => mm_interconnect_1_framewriter_0_avalon_slave_readdata,      --               .readdata
			avalon_ss_waitrequest   => mm_interconnect_1_framewriter_0_avalon_slave_waitrequest,   --               .waitrequest
			avalon_ss_readdatavalid => mm_interconnect_1_framewriter_0_avalon_slave_readdatavalid, --               .readdatavalid
			avalon_ss_write         => mm_interconnect_1_framewriter_0_avalon_slave_write,         --               .write
			avalon_ss_writedata     => mm_interconnect_1_framewriter_0_avalon_slave_writedata,     --               .writedata
			avalon_st_data          => pico640_ctrl_0_avalon_st_out_data,                          --   avalon_st_in.data
			avalon_st_endofpacket   => pico640_ctrl_0_avalon_st_out_endofpacket,                   --               .endofpacket
			avalon_st_ready         => pico640_ctrl_0_avalon_st_out_ready,                         --               .ready
			avalon_st_startofpacket => pico640_ctrl_0_avalon_st_out_startofpacket,                 --               .startofpacket
			avalon_st_valid         => pico640_ctrl_0_avalon_st_out_valid                          --               .valid
		);

	hps_0 : component cycloneV_soc_hps_0
		generic map (
			F2S_Width => 3,
			S2F_Width => 2
		)
		port map (
			mem_a                    => memory_mem_a,                                        --            memory.mem_a
			mem_ba                   => memory_mem_ba,                                       --                  .mem_ba
			mem_ck                   => memory_mem_ck,                                       --                  .mem_ck
			mem_ck_n                 => memory_mem_ck_n,                                     --                  .mem_ck_n
			mem_cke                  => memory_mem_cke,                                      --                  .mem_cke
			mem_cs_n                 => memory_mem_cs_n,                                     --                  .mem_cs_n
			mem_ras_n                => memory_mem_ras_n,                                    --                  .mem_ras_n
			mem_cas_n                => memory_mem_cas_n,                                    --                  .mem_cas_n
			mem_we_n                 => memory_mem_we_n,                                     --                  .mem_we_n
			mem_reset_n              => memory_mem_reset_n,                                  --                  .mem_reset_n
			mem_dq                   => memory_mem_dq,                                       --                  .mem_dq
			mem_dqs                  => memory_mem_dqs,                                      --                  .mem_dqs
			mem_dqs_n                => memory_mem_dqs_n,                                    --                  .mem_dqs_n
			mem_odt                  => memory_mem_odt,                                      --                  .mem_odt
			mem_dm                   => memory_mem_dm,                                       --                  .mem_dm
			oct_rzqin                => memory_oct_rzqin,                                    --                  .oct_rzqin
			hps_io_emac1_inst_TX_CLK => hps_io_hps_io_emac1_inst_TX_CLK,                     --            hps_io.hps_io_emac1_inst_TX_CLK
			hps_io_emac1_inst_TXD0   => hps_io_hps_io_emac1_inst_TXD0,                       --                  .hps_io_emac1_inst_TXD0
			hps_io_emac1_inst_TXD1   => hps_io_hps_io_emac1_inst_TXD1,                       --                  .hps_io_emac1_inst_TXD1
			hps_io_emac1_inst_TXD2   => hps_io_hps_io_emac1_inst_TXD2,                       --                  .hps_io_emac1_inst_TXD2
			hps_io_emac1_inst_TXD3   => hps_io_hps_io_emac1_inst_TXD3,                       --                  .hps_io_emac1_inst_TXD3
			hps_io_emac1_inst_RXD0   => hps_io_hps_io_emac1_inst_RXD0,                       --                  .hps_io_emac1_inst_RXD0
			hps_io_emac1_inst_MDIO   => hps_io_hps_io_emac1_inst_MDIO,                       --                  .hps_io_emac1_inst_MDIO
			hps_io_emac1_inst_MDC    => hps_io_hps_io_emac1_inst_MDC,                        --                  .hps_io_emac1_inst_MDC
			hps_io_emac1_inst_RX_CTL => hps_io_hps_io_emac1_inst_RX_CTL,                     --                  .hps_io_emac1_inst_RX_CTL
			hps_io_emac1_inst_TX_CTL => hps_io_hps_io_emac1_inst_TX_CTL,                     --                  .hps_io_emac1_inst_TX_CTL
			hps_io_emac1_inst_RX_CLK => hps_io_hps_io_emac1_inst_RX_CLK,                     --                  .hps_io_emac1_inst_RX_CLK
			hps_io_emac1_inst_RXD1   => hps_io_hps_io_emac1_inst_RXD1,                       --                  .hps_io_emac1_inst_RXD1
			hps_io_emac1_inst_RXD2   => hps_io_hps_io_emac1_inst_RXD2,                       --                  .hps_io_emac1_inst_RXD2
			hps_io_emac1_inst_RXD3   => hps_io_hps_io_emac1_inst_RXD3,                       --                  .hps_io_emac1_inst_RXD3
			hps_io_sdio_inst_CMD     => hps_io_hps_io_sdio_inst_CMD,                         --                  .hps_io_sdio_inst_CMD
			hps_io_sdio_inst_D0      => hps_io_hps_io_sdio_inst_D0,                          --                  .hps_io_sdio_inst_D0
			hps_io_sdio_inst_D1      => hps_io_hps_io_sdio_inst_D1,                          --                  .hps_io_sdio_inst_D1
			hps_io_sdio_inst_CLK     => hps_io_hps_io_sdio_inst_CLK,                         --                  .hps_io_sdio_inst_CLK
			hps_io_sdio_inst_D2      => hps_io_hps_io_sdio_inst_D2,                          --                  .hps_io_sdio_inst_D2
			hps_io_sdio_inst_D3      => hps_io_hps_io_sdio_inst_D3,                          --                  .hps_io_sdio_inst_D3
			hps_io_usb1_inst_D0      => hps_io_hps_io_usb1_inst_D0,                          --                  .hps_io_usb1_inst_D0
			hps_io_usb1_inst_D1      => hps_io_hps_io_usb1_inst_D1,                          --                  .hps_io_usb1_inst_D1
			hps_io_usb1_inst_D2      => hps_io_hps_io_usb1_inst_D2,                          --                  .hps_io_usb1_inst_D2
			hps_io_usb1_inst_D3      => hps_io_hps_io_usb1_inst_D3,                          --                  .hps_io_usb1_inst_D3
			hps_io_usb1_inst_D4      => hps_io_hps_io_usb1_inst_D4,                          --                  .hps_io_usb1_inst_D4
			hps_io_usb1_inst_D5      => hps_io_hps_io_usb1_inst_D5,                          --                  .hps_io_usb1_inst_D5
			hps_io_usb1_inst_D6      => hps_io_hps_io_usb1_inst_D6,                          --                  .hps_io_usb1_inst_D6
			hps_io_usb1_inst_D7      => hps_io_hps_io_usb1_inst_D7,                          --                  .hps_io_usb1_inst_D7
			hps_io_usb1_inst_CLK     => hps_io_hps_io_usb1_inst_CLK,                         --                  .hps_io_usb1_inst_CLK
			hps_io_usb1_inst_STP     => hps_io_hps_io_usb1_inst_STP,                         --                  .hps_io_usb1_inst_STP
			hps_io_usb1_inst_DIR     => hps_io_hps_io_usb1_inst_DIR,                         --                  .hps_io_usb1_inst_DIR
			hps_io_usb1_inst_NXT     => hps_io_hps_io_usb1_inst_NXT,                         --                  .hps_io_usb1_inst_NXT
			hps_io_uart0_inst_RX     => hps_io_hps_io_uart0_inst_RX,                         --                  .hps_io_uart0_inst_RX
			hps_io_uart0_inst_TX     => hps_io_hps_io_uart0_inst_TX,                         --                  .hps_io_uart0_inst_TX
			h2f_rst_n                => hps_0_h2f_reset_reset,                               --         h2f_reset.reset_n
			f2h_sdram0_clk           => clk_clk,                                             --  f2h_sdram0_clock.clk
			f2h_sdram0_ADDRESS       => mm_interconnect_0_hps_0_f2h_sdram0_data_address,     --   f2h_sdram0_data.address
			f2h_sdram0_BURSTCOUNT    => mm_interconnect_0_hps_0_f2h_sdram0_data_burstcount,  --                  .burstcount
			f2h_sdram0_WAITREQUEST   => mm_interconnect_0_hps_0_f2h_sdram0_data_waitrequest, --                  .waitrequest
			f2h_sdram0_WRITEDATA     => mm_interconnect_0_hps_0_f2h_sdram0_data_writedata,   --                  .writedata
			f2h_sdram0_BYTEENABLE    => mm_interconnect_0_hps_0_f2h_sdram0_data_byteenable,  --                  .byteenable
			f2h_sdram0_WRITE         => mm_interconnect_0_hps_0_f2h_sdram0_data_write,       --                  .write
			h2f_axi_clk              => clk_clk,                                             --     h2f_axi_clock.clk
			h2f_AWID                 => open,                                                --    h2f_axi_master.awid
			h2f_AWADDR               => open,                                                --                  .awaddr
			h2f_AWLEN                => open,                                                --                  .awlen
			h2f_AWSIZE               => open,                                                --                  .awsize
			h2f_AWBURST              => open,                                                --                  .awburst
			h2f_AWLOCK               => open,                                                --                  .awlock
			h2f_AWCACHE              => open,                                                --                  .awcache
			h2f_AWPROT               => open,                                                --                  .awprot
			h2f_AWVALID              => open,                                                --                  .awvalid
			h2f_AWREADY              => open,                                                --                  .awready
			h2f_WID                  => open,                                                --                  .wid
			h2f_WDATA                => open,                                                --                  .wdata
			h2f_WSTRB                => open,                                                --                  .wstrb
			h2f_WLAST                => open,                                                --                  .wlast
			h2f_WVALID               => open,                                                --                  .wvalid
			h2f_WREADY               => open,                                                --                  .wready
			h2f_BID                  => open,                                                --                  .bid
			h2f_BRESP                => open,                                                --                  .bresp
			h2f_BVALID               => open,                                                --                  .bvalid
			h2f_BREADY               => open,                                                --                  .bready
			h2f_ARID                 => open,                                                --                  .arid
			h2f_ARADDR               => open,                                                --                  .araddr
			h2f_ARLEN                => open,                                                --                  .arlen
			h2f_ARSIZE               => open,                                                --                  .arsize
			h2f_ARBURST              => open,                                                --                  .arburst
			h2f_ARLOCK               => open,                                                --                  .arlock
			h2f_ARCACHE              => open,                                                --                  .arcache
			h2f_ARPROT               => open,                                                --                  .arprot
			h2f_ARVALID              => open,                                                --                  .arvalid
			h2f_ARREADY              => open,                                                --                  .arready
			h2f_RID                  => open,                                                --                  .rid
			h2f_RDATA                => open,                                                --                  .rdata
			h2f_RRESP                => open,                                                --                  .rresp
			h2f_RLAST                => open,                                                --                  .rlast
			h2f_RVALID               => open,                                                --                  .rvalid
			h2f_RREADY               => open,                                                --                  .rready
			f2h_axi_clk              => clk_clk,                                             --     f2h_axi_clock.clk
			f2h_AWID                 => open,                                                --     f2h_axi_slave.awid
			f2h_AWADDR               => open,                                                --                  .awaddr
			f2h_AWLEN                => open,                                                --                  .awlen
			f2h_AWSIZE               => open,                                                --                  .awsize
			f2h_AWBURST              => open,                                                --                  .awburst
			f2h_AWLOCK               => open,                                                --                  .awlock
			f2h_AWCACHE              => open,                                                --                  .awcache
			f2h_AWPROT               => open,                                                --                  .awprot
			f2h_AWVALID              => open,                                                --                  .awvalid
			f2h_AWREADY              => open,                                                --                  .awready
			f2h_AWUSER               => open,                                                --                  .awuser
			f2h_WID                  => open,                                                --                  .wid
			f2h_WDATA                => open,                                                --                  .wdata
			f2h_WSTRB                => open,                                                --                  .wstrb
			f2h_WLAST                => open,                                                --                  .wlast
			f2h_WVALID               => open,                                                --                  .wvalid
			f2h_WREADY               => open,                                                --                  .wready
			f2h_BID                  => open,                                                --                  .bid
			f2h_BRESP                => open,                                                --                  .bresp
			f2h_BVALID               => open,                                                --                  .bvalid
			f2h_BREADY               => open,                                                --                  .bready
			f2h_ARID                 => open,                                                --                  .arid
			f2h_ARADDR               => open,                                                --                  .araddr
			f2h_ARLEN                => open,                                                --                  .arlen
			f2h_ARSIZE               => open,                                                --                  .arsize
			f2h_ARBURST              => open,                                                --                  .arburst
			f2h_ARLOCK               => open,                                                --                  .arlock
			f2h_ARCACHE              => open,                                                --                  .arcache
			f2h_ARPROT               => open,                                                --                  .arprot
			f2h_ARVALID              => open,                                                --                  .arvalid
			f2h_ARREADY              => open,                                                --                  .arready
			f2h_ARUSER               => open,                                                --                  .aruser
			f2h_RID                  => open,                                                --                  .rid
			f2h_RDATA                => open,                                                --                  .rdata
			f2h_RRESP                => open,                                                --                  .rresp
			f2h_RLAST                => open,                                                --                  .rlast
			f2h_RVALID               => open,                                                --                  .rvalid
			f2h_RREADY               => open,                                                --                  .rready
			h2f_lw_axi_clk           => clk_clk,                                             --  h2f_lw_axi_clock.clk
			h2f_lw_AWID              => hps_0_h2f_lw_axi_master_awid,                        -- h2f_lw_axi_master.awid
			h2f_lw_AWADDR            => hps_0_h2f_lw_axi_master_awaddr,                      --                  .awaddr
			h2f_lw_AWLEN             => hps_0_h2f_lw_axi_master_awlen,                       --                  .awlen
			h2f_lw_AWSIZE            => hps_0_h2f_lw_axi_master_awsize,                      --                  .awsize
			h2f_lw_AWBURST           => hps_0_h2f_lw_axi_master_awburst,                     --                  .awburst
			h2f_lw_AWLOCK            => hps_0_h2f_lw_axi_master_awlock,                      --                  .awlock
			h2f_lw_AWCACHE           => hps_0_h2f_lw_axi_master_awcache,                     --                  .awcache
			h2f_lw_AWPROT            => hps_0_h2f_lw_axi_master_awprot,                      --                  .awprot
			h2f_lw_AWVALID           => hps_0_h2f_lw_axi_master_awvalid,                     --                  .awvalid
			h2f_lw_AWREADY           => hps_0_h2f_lw_axi_master_awready,                     --                  .awready
			h2f_lw_WID               => hps_0_h2f_lw_axi_master_wid,                         --                  .wid
			h2f_lw_WDATA             => hps_0_h2f_lw_axi_master_wdata,                       --                  .wdata
			h2f_lw_WSTRB             => hps_0_h2f_lw_axi_master_wstrb,                       --                  .wstrb
			h2f_lw_WLAST             => hps_0_h2f_lw_axi_master_wlast,                       --                  .wlast
			h2f_lw_WVALID            => hps_0_h2f_lw_axi_master_wvalid,                      --                  .wvalid
			h2f_lw_WREADY            => hps_0_h2f_lw_axi_master_wready,                      --                  .wready
			h2f_lw_BID               => hps_0_h2f_lw_axi_master_bid,                         --                  .bid
			h2f_lw_BRESP             => hps_0_h2f_lw_axi_master_bresp,                       --                  .bresp
			h2f_lw_BVALID            => hps_0_h2f_lw_axi_master_bvalid,                      --                  .bvalid
			h2f_lw_BREADY            => hps_0_h2f_lw_axi_master_bready,                      --                  .bready
			h2f_lw_ARID              => hps_0_h2f_lw_axi_master_arid,                        --                  .arid
			h2f_lw_ARADDR            => hps_0_h2f_lw_axi_master_araddr,                      --                  .araddr
			h2f_lw_ARLEN             => hps_0_h2f_lw_axi_master_arlen,                       --                  .arlen
			h2f_lw_ARSIZE            => hps_0_h2f_lw_axi_master_arsize,                      --                  .arsize
			h2f_lw_ARBURST           => hps_0_h2f_lw_axi_master_arburst,                     --                  .arburst
			h2f_lw_ARLOCK            => hps_0_h2f_lw_axi_master_arlock,                      --                  .arlock
			h2f_lw_ARCACHE           => hps_0_h2f_lw_axi_master_arcache,                     --                  .arcache
			h2f_lw_ARPROT            => hps_0_h2f_lw_axi_master_arprot,                      --                  .arprot
			h2f_lw_ARVALID           => hps_0_h2f_lw_axi_master_arvalid,                     --                  .arvalid
			h2f_lw_ARREADY           => hps_0_h2f_lw_axi_master_arready,                     --                  .arready
			h2f_lw_RID               => hps_0_h2f_lw_axi_master_rid,                         --                  .rid
			h2f_lw_RDATA             => hps_0_h2f_lw_axi_master_rdata,                       --                  .rdata
			h2f_lw_RRESP             => hps_0_h2f_lw_axi_master_rresp,                       --                  .rresp
			h2f_lw_RLAST             => hps_0_h2f_lw_axi_master_rlast,                       --                  .rlast
			h2f_lw_RVALID            => hps_0_h2f_lw_axi_master_rvalid,                      --                  .rvalid
			h2f_lw_RREADY            => hps_0_h2f_lw_axi_master_rready                       --                  .rready
		);

	i2c_master_avalon_0 : component i2c_master_avalon
		generic map (
			CLOCK_FREQ   => 50000000,
			I2C_CLK_FREQ => 200000,
			CHECK_ACK    => true
		)
		port map (
			clk                 => clk_clk,                                                   --       clock.clk
			slave_chipselect    => mm_interconnect_1_i2c_master_avalon_0_slave_chipselect,    --       slave.chipselect
			slave_write         => mm_interconnect_1_i2c_master_avalon_0_slave_write,         --            .write
			slave_address       => mm_interconnect_1_i2c_master_avalon_0_slave_address,       --            .address
			slave_writedata     => mm_interconnect_1_i2c_master_avalon_0_slave_writedata,     --            .writedata
			slave_waitrequest   => mm_interconnect_1_i2c_master_avalon_0_slave_waitrequest,   --            .waitrequest
			slave_readdatavalid => mm_interconnect_1_i2c_master_avalon_0_slave_readdatavalid, --            .readdatavalid
			slave_readdata      => mm_interconnect_1_i2c_master_avalon_0_slave_readdata,      --            .readdata
			slave_read          => mm_interconnect_1_i2c_master_avalon_0_slave_read,          --            .read
			rst_n               => rst_controller_reset_out_reset_ports_inv,                  --  reset_sink.reset_n
			SCL                 => i2c_SCL,                                                   -- conduit_end.export
			SDA                 => i2c_SDA                                                    --            .export
		);

	led : component cycloneV_soc_led
		port map (
			clk        => clk_clk,                                  --                 clk.clk
			reset_n    => rst_controller_reset_out_reset_ports_inv, --               reset.reset_n
			address    => mm_interconnect_1_led_s1_address,         --                  s1.address
			write_n    => mm_interconnect_1_led_s1_write_ports_inv, --                    .write_n
			writedata  => mm_interconnect_1_led_s1_writedata,       --                    .writedata
			chipselect => mm_interconnect_1_led_s1_chipselect,      --                    .chipselect
			readdata   => mm_interconnect_1_led_s1_readdata,        --                    .readdata
			out_port   => led_external_connection_export            -- external_connection.export
		);

	pico640_ctrl_0 : component pico640_avalon
		generic map (
			SENSOR_CLOCK => 38000000
		)
		port map (
			PSYNC                   => pico640_PSYNC,                                               --        conduit.export
			VSYNC                   => pico640_VSYNC,                                               --               .export
			HSYNC                   => pico640_HSYNC,                                               --               .export
			ADC_DATA                => pico640_ADC_DATA,                                            --               .export
			SHUTTER                 => pico640_SHUTTER,                                             --               .export
			SENSOR_RST_N            => pico640_SENSOR_RST_N,                                        --               .export
			CLOCK_EN                => pico640_CLOCK_EN,                                            --               .export
			avalon_ss_clk           => clk_clk,                                                     --  avalon_ss_clk.clk
			master_clk              => pll_0_outclk0_clk,                                           --         mc_clk.clk
			avalon_ss_rstn          => rst_controller_reset_out_reset_ports_inv,                    -- avalon_ss_rstn.reset_n
			master_rstn             => rst_controller_001_reset_out_reset_ports_inv,                --        mc_rstn.reset_n
			avalon_st_startofpacket => pico640_ctrl_0_avalon_st_out_startofpacket,                  --  avalon_st_out.startofpacket
			avalon_st_endofpacket   => pico640_ctrl_0_avalon_st_out_endofpacket,                    --               .endofpacket
			avalon_st_valid         => pico640_ctrl_0_avalon_st_out_valid,                          --               .valid
			avalon_st_data          => pico640_ctrl_0_avalon_st_out_data,                           --               .data
			avalon_st_ready         => pico640_ctrl_0_avalon_st_out_ready,                          --               .ready
			slave_write             => mm_interconnect_1_pico640_ctrl_0_avalon_slave_write,         --   avalon_slave.write
			slave_address           => mm_interconnect_1_pico640_ctrl_0_avalon_slave_address,       --               .address
			slave_writedata         => mm_interconnect_1_pico640_ctrl_0_avalon_slave_writedata,     --               .writedata
			slave_waitrequest       => mm_interconnect_1_pico640_ctrl_0_avalon_slave_waitrequest,   --               .waitrequest
			slave_readdatavalid     => mm_interconnect_1_pico640_ctrl_0_avalon_slave_readdatavalid, --               .readdatavalid
			slave_readdata          => mm_interconnect_1_pico640_ctrl_0_avalon_slave_readdata,      --               .readdata
			slave_read              => mm_interconnect_1_pico640_ctrl_0_avalon_slave_read           --               .read
		);

	pio_0 : component cycloneV_soc_led
		port map (
			clk        => clk_clk,                                    --                 clk.clk
			reset_n    => rst_controller_reset_out_reset_ports_inv,   --               reset.reset_n
			address    => mm_interconnect_1_pio_0_s1_address,         --                  s1.address
			write_n    => mm_interconnect_1_pio_0_s1_write_ports_inv, --                    .write_n
			writedata  => mm_interconnect_1_pio_0_s1_writedata,       --                    .writedata
			chipselect => mm_interconnect_1_pio_0_s1_chipselect,      --                    .chipselect
			readdata   => mm_interconnect_1_pio_0_s1_readdata,        --                    .readdata
			out_port   => pio_export                                  -- external_connection.export
		);

	pll_0 : component cycloneV_soc_pll_0
		port map (
			refclk   => clk_clk,                 --  refclk.clk
			rst      => reset_reset_n_ports_inv, --   reset.reset
			outclk_0 => pll_0_outclk0_clk,       -- outclk0.clk
			outclk_1 => adc_clk,                 -- outclk1.clk
			locked   => open                     -- (terminated)
		);

	sw : component cycloneV_soc_sw
		port map (
			clk      => clk_clk,                                  --                 clk.clk
			reset_n  => rst_controller_reset_out_reset_ports_inv, --               reset.reset_n
			address  => mm_interconnect_1_sw_s1_address,          --                  s1.address
			readdata => mm_interconnect_1_sw_s1_readdata,         --                    .readdata
			in_port  => sw_external_connection_export             -- external_connection.export
		);

	mm_interconnect_0 : component cycloneV_soc_mm_interconnect_0
		port map (
			clock_50_clk_clk                                                   => clk_clk,                                             --                                                 clock_50_clk.clk
			framewriter_0_avalon_mm_rstn_reset_bridge_in_reset_reset           => rst_controller_reset_out_reset,                      --           framewriter_0_avalon_mm_rstn_reset_bridge_in_reset.reset
			hps_0_f2h_sdram0_data_translator_reset_reset_bridge_in_reset_reset => rst_controller_002_reset_out_reset,                  -- hps_0_f2h_sdram0_data_translator_reset_reset_bridge_in_reset.reset
			framewriter_0_avalon_master_address                                => framewriter_0_avalon_master_address,                 --                                  framewriter_0_avalon_master.address
			framewriter_0_avalon_master_waitrequest                            => framewriter_0_avalon_master_waitrequest,             --                                                             .waitrequest
			framewriter_0_avalon_master_burstcount                             => framewriter_0_avalon_master_burstcount,              --                                                             .burstcount
			framewriter_0_avalon_master_write                                  => framewriter_0_avalon_master_write,                   --                                                             .write
			framewriter_0_avalon_master_writedata                              => framewriter_0_avalon_master_writedata,               --                                                             .writedata
			hps_0_f2h_sdram0_data_address                                      => mm_interconnect_0_hps_0_f2h_sdram0_data_address,     --                                        hps_0_f2h_sdram0_data.address
			hps_0_f2h_sdram0_data_write                                        => mm_interconnect_0_hps_0_f2h_sdram0_data_write,       --                                                             .write
			hps_0_f2h_sdram0_data_writedata                                    => mm_interconnect_0_hps_0_f2h_sdram0_data_writedata,   --                                                             .writedata
			hps_0_f2h_sdram0_data_burstcount                                   => mm_interconnect_0_hps_0_f2h_sdram0_data_burstcount,  --                                                             .burstcount
			hps_0_f2h_sdram0_data_byteenable                                   => mm_interconnect_0_hps_0_f2h_sdram0_data_byteenable,  --                                                             .byteenable
			hps_0_f2h_sdram0_data_waitrequest                                  => mm_interconnect_0_hps_0_f2h_sdram0_data_waitrequest  --                                                             .waitrequest
		);

	mm_interconnect_1 : component cycloneV_soc_mm_interconnect_1
		port map (
			hps_0_h2f_lw_axi_master_awid                                        => hps_0_h2f_lw_axi_master_awid,                                --                                       hps_0_h2f_lw_axi_master.awid
			hps_0_h2f_lw_axi_master_awaddr                                      => hps_0_h2f_lw_axi_master_awaddr,                              --                                                              .awaddr
			hps_0_h2f_lw_axi_master_awlen                                       => hps_0_h2f_lw_axi_master_awlen,                               --                                                              .awlen
			hps_0_h2f_lw_axi_master_awsize                                      => hps_0_h2f_lw_axi_master_awsize,                              --                                                              .awsize
			hps_0_h2f_lw_axi_master_awburst                                     => hps_0_h2f_lw_axi_master_awburst,                             --                                                              .awburst
			hps_0_h2f_lw_axi_master_awlock                                      => hps_0_h2f_lw_axi_master_awlock,                              --                                                              .awlock
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
			hps_0_h2f_lw_axi_master_arprot                                      => hps_0_h2f_lw_axi_master_arprot,                              --                                                              .arprot
			hps_0_h2f_lw_axi_master_arvalid                                     => hps_0_h2f_lw_axi_master_arvalid,                             --                                                              .arvalid
			hps_0_h2f_lw_axi_master_arready                                     => hps_0_h2f_lw_axi_master_arready,                             --                                                              .arready
			hps_0_h2f_lw_axi_master_rid                                         => hps_0_h2f_lw_axi_master_rid,                                 --                                                              .rid
			hps_0_h2f_lw_axi_master_rdata                                       => hps_0_h2f_lw_axi_master_rdata,                               --                                                              .rdata
			hps_0_h2f_lw_axi_master_rresp                                       => hps_0_h2f_lw_axi_master_rresp,                               --                                                              .rresp
			hps_0_h2f_lw_axi_master_rlast                                       => hps_0_h2f_lw_axi_master_rlast,                               --                                                              .rlast
			hps_0_h2f_lw_axi_master_rvalid                                      => hps_0_h2f_lw_axi_master_rvalid,                              --                                                              .rvalid
			hps_0_h2f_lw_axi_master_rready                                      => hps_0_h2f_lw_axi_master_rready,                              --                                                              .rready
			clock_50_clk_clk                                                    => clk_clk,                                                     --                                                  clock_50_clk.clk
			framewriter_0_avalon_ss_rstn_reset_bridge_in_reset_reset            => rst_controller_reset_out_reset,                              --            framewriter_0_avalon_ss_rstn_reset_bridge_in_reset.reset
			hps_0_h2f_lw_axi_master_agent_clk_reset_reset_bridge_in_reset_reset => rst_controller_002_reset_out_reset,                          -- hps_0_h2f_lw_axi_master_agent_clk_reset_reset_bridge_in_reset.reset
			framewriter_0_avalon_slave_address                                  => mm_interconnect_1_framewriter_0_avalon_slave_address,        --                                    framewriter_0_avalon_slave.address
			framewriter_0_avalon_slave_write                                    => mm_interconnect_1_framewriter_0_avalon_slave_write,          --                                                              .write
			framewriter_0_avalon_slave_read                                     => mm_interconnect_1_framewriter_0_avalon_slave_read,           --                                                              .read
			framewriter_0_avalon_slave_readdata                                 => mm_interconnect_1_framewriter_0_avalon_slave_readdata,       --                                                              .readdata
			framewriter_0_avalon_slave_writedata                                => mm_interconnect_1_framewriter_0_avalon_slave_writedata,      --                                                              .writedata
			framewriter_0_avalon_slave_readdatavalid                            => mm_interconnect_1_framewriter_0_avalon_slave_readdatavalid,  --                                                              .readdatavalid
			framewriter_0_avalon_slave_waitrequest                              => mm_interconnect_1_framewriter_0_avalon_slave_waitrequest,    --                                                              .waitrequest
			i2c_master_avalon_0_slave_address                                   => mm_interconnect_1_i2c_master_avalon_0_slave_address,         --                                     i2c_master_avalon_0_slave.address
			i2c_master_avalon_0_slave_write                                     => mm_interconnect_1_i2c_master_avalon_0_slave_write,           --                                                              .write
			i2c_master_avalon_0_slave_read                                      => mm_interconnect_1_i2c_master_avalon_0_slave_read,            --                                                              .read
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
			pio_0_s1_writedata                                                  => mm_interconnect_1_pio_0_s1_writedata,                        --                                                              .writedata
			pio_0_s1_chipselect                                                 => mm_interconnect_1_pio_0_s1_chipselect,                       --                                                              .chipselect
			sw_s1_address                                                       => mm_interconnect_1_sw_s1_address,                             --                                                         sw_s1.address
			sw_s1_readdata                                                      => mm_interconnect_1_sw_s1_readdata                             --                                                              .readdata
		);

	rst_controller : component altera_reset_controller
		generic map (
			NUM_RESET_INPUTS          => 1,
			OUTPUT_RESET_SYNC_EDGES   => "deassert",
			SYNC_DEPTH                => 2,
			RESET_REQUEST_PRESENT     => 0,
			RESET_REQ_WAIT_TIME       => 1,
			MIN_RST_ASSERTION_TIME    => 3,
			RESET_REQ_EARLY_DSRT_TIME => 1,
			USE_RESET_REQUEST_IN0     => 0,
			USE_RESET_REQUEST_IN1     => 0,
			USE_RESET_REQUEST_IN2     => 0,
			USE_RESET_REQUEST_IN3     => 0,
			USE_RESET_REQUEST_IN4     => 0,
			USE_RESET_REQUEST_IN5     => 0,
			USE_RESET_REQUEST_IN6     => 0,
			USE_RESET_REQUEST_IN7     => 0,
			USE_RESET_REQUEST_IN8     => 0,
			USE_RESET_REQUEST_IN9     => 0,
			USE_RESET_REQUEST_IN10    => 0,
			USE_RESET_REQUEST_IN11    => 0,
			USE_RESET_REQUEST_IN12    => 0,
			USE_RESET_REQUEST_IN13    => 0,
			USE_RESET_REQUEST_IN14    => 0,
			USE_RESET_REQUEST_IN15    => 0,
			ADAPT_RESET_REQUEST       => 0
		)
		port map (
			reset_in0      => reset_reset_n_ports_inv,        -- reset_in0.reset
			clk            => clk_clk,                        --       clk.clk
			reset_out      => rst_controller_reset_out_reset, -- reset_out.reset
			reset_req      => open,                           -- (terminated)
			reset_req_in0  => '0',                            -- (terminated)
			reset_in1      => '0',                            -- (terminated)
			reset_req_in1  => '0',                            -- (terminated)
			reset_in2      => '0',                            -- (terminated)
			reset_req_in2  => '0',                            -- (terminated)
			reset_in3      => '0',                            -- (terminated)
			reset_req_in3  => '0',                            -- (terminated)
			reset_in4      => '0',                            -- (terminated)
			reset_req_in4  => '0',                            -- (terminated)
			reset_in5      => '0',                            -- (terminated)
			reset_req_in5  => '0',                            -- (terminated)
			reset_in6      => '0',                            -- (terminated)
			reset_req_in6  => '0',                            -- (terminated)
			reset_in7      => '0',                            -- (terminated)
			reset_req_in7  => '0',                            -- (terminated)
			reset_in8      => '0',                            -- (terminated)
			reset_req_in8  => '0',                            -- (terminated)
			reset_in9      => '0',                            -- (terminated)
			reset_req_in9  => '0',                            -- (terminated)
			reset_in10     => '0',                            -- (terminated)
			reset_req_in10 => '0',                            -- (terminated)
			reset_in11     => '0',                            -- (terminated)
			reset_req_in11 => '0',                            -- (terminated)
			reset_in12     => '0',                            -- (terminated)
			reset_req_in12 => '0',                            -- (terminated)
			reset_in13     => '0',                            -- (terminated)
			reset_req_in13 => '0',                            -- (terminated)
			reset_in14     => '0',                            -- (terminated)
			reset_req_in14 => '0',                            -- (terminated)
			reset_in15     => '0',                            -- (terminated)
			reset_req_in15 => '0'                             -- (terminated)
		);
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
